Ferro-Giconi/Neopixel-bitmap/NeopixelBitmap.py

# Waveshare 160 Neopixel Board Basic
# Tony Goodhew 19th April 2022 for thepihut.com
import array
import utime
from machine import ADC, Pin
import rp2
import random
import math
import micropython
import _thread


# ==================================== battery ===================================
# reads the battery voltage on pin GP26 which is ADC0 on the Tiny2040
vsys = ADC(26)
# conversion factor to convert the output into a voltage. This uses a voltage
# divider to divide the voltage reading in half so it multiplies by 2.
conversion_factor = 2 * 3.3 / 65535
# these still need to be tuned based on what the ADC pin actually sees
full_battery = 4.2
empty_battery = 3.3
# convert the raw ADC read into a voltage, and then a percentage
battery_voltage = vsys.read_u16() * conversion_factor
battery_percentage = 100 * ((battery_voltage - empty_battery) / (full_battery - empty_battery))
if battery_percentage > 100:
    battery_percentage = 100.00

# battery voltage and percengate.
print('{:.2f}'.format(battery_voltage) + "v   -   " + '{:.0f}%'.format(battery_percentage))

# ==================================== screen stuff ===================================
# in variable names: w = width on the x axis and h = height on the y axis

# define how many Neopixels you have, width and height
# when connecting multiple Neopixels, arrange them in order from left to right, then top to bottom.
global screens_w
screens_w = 2
global screens_h
screens_h = 1
# if there is a gap between Neopixels, define the gap size in number of LEDs.
# this will take gaps into account when displaying images or text for a more normal look.
# gap_w = gap width in number of pixels between horizontally places Neopixels
# gap_h = gap height in number of pixels between vertically stacked Neopixels
# Integer only. Decimals will probably break it.
global gap_w
gap_w = 0
global gap_h
gap_h = 0

# I couldn't figure out how to check if the second thread is locked correctly so instead I'm using a global variable
global threadLocked
threadLocked = False

# Configure the number of WS2812 LEDs.
PIN_NUM = 6
brightness = 0.1
# set total number of LEDs. Each neopixel has 160 LEDs, 10H 16W.
screen_total_width = screens_w * 16 + (screens_w * gap_w - gap_w)
screen_total_height = screens_h * 10 + (screens_h * gap_h - gap_h)
NUM_LEDS = screen_total_width * screen_total_height

#calculates which X and Y cordinates will not be used if there are gaps defined
global missing_x
missing_x = []
for i in range(16,screen_total_width+1,1):
    ii = i
    while ii > 16:
        ii = ii - 16 - gap_w
    if ii <= 0:
        missing_x.append(i)

global missing_y
missing_y = []
for i in range(10,screen_total_height+1,1):
    ii = i
    while ii > 10:
        ii = ii - 10 - gap_h
    if ii <= 0:
        missing_y.append(i)

# Boilerplate Neopixel driver for RP2040
@rp2.asm_pio(sideset_init=rp2.PIO.OUT_LOW, out_shiftdir=rp2.PIO.SHIFT_LEFT, autopull=True, pull_thresh=24)
def ws2812():
    T1 = 2
    T2 = 5
    T3 = 3
    wrap_target()
    label("bitloop")
    out(x, 1)               .side(0)    [T3 - 1]
    jmp(not_x, "do_zero")   .side(1)    [T1 - 1]
    jmp("bitloop")          .side(1)    [T2 - 1]
    label("do_zero")
    nop()                   .side(0)    [T2 - 1]
    wrap()

# Create the StateMachine with the ws2812 program, outputting on pin
# You can also increase the frequency to improve performance by 1-2ms
sm = rp2.StateMachine(0, ws2812, freq=8_000_000, sideset_base=Pin(PIN_NUM))

# Start the StateMachine, it will wait for data on its FIFO.
sm.active(1)

# Display a pattern on the LEDs via an array of LED RGB values.
ar = array.array("I", [0 for _ in range(NUM_LEDS)])

####################### Functions ##############################

def pixels_show():
    dimmer_ar = array.array("I", [0 for _ in range(NUM_LEDS)])
    for i,c in enumerate(ar):
        r = int(((c >> 8) & 0xFF) * brightness)
        g = int(((c >> 16) & 0xFF) * brightness)
        b = int((c & 0xFF) * brightness)
        dimmer_ar[i] = (g<<16) + (r<<8) + b
    sm.put(dimmer_ar, 8)

def pixels_set(i, colour):
    ar[i] = (colour[1]<<16) + (colour[0]<<8) + colour[2]

def xy_set(x, y, colour):
    #check if a pixel is valid and set it if it is
    if valid_pixel(x,y):
        xy_set_valid(x, y, colour)

def xy_set_valid(x, y, colour):
    # +1 to x and y allows me to do pixel math in this function starting at 1 when the input x and y start at 0.
    # it's just easier for me to figure out the math that way.
    
    x = x + 1
    y = y + 1

    screen_x = 1
    screen_y = 1
    xx = x
    yy = y
    while xx > 16:
        screen_x = screen_x + 1
        xx = xx - 16 - gap_w
    while yy > 10:
        screen_y = screen_y + 1
        yy = yy - 10 - gap_h
    screen_number = screen_x + ((screen_y - 1) * screens_w)
    
    #calculate which pixel to set on which Neopixel
    pos = ((screen_number - 1) * 160) + (xx - 1) + (yy - 1) * 16
    pixels_set(pos, colour)

# it seems silly to do this but anything that can save an operation two in the valid pixel check will
# help improve how many μs each frame takes to display
global screen_total_width_minus_one
screen_total_width_minus_one = screen_total_width - 1
global screen_total_height_minus_one
screen_total_height_minus_one = screen_total_height - 1
def valid_pixel(x,y):
    # check if a pixel is valid
    valid_pixel = True
    # Check if the pixel you want to set is outside the size of the
    # screen to avoid wasting CPU cycles on pixels that you can't see
    if (x<0) or (y<0) or (x > screen_total_width_minus_one) or (y > screen_total_height_minus_one):
        valid_pixel = False
    # If you configured a gap between neopixels, check if the pixel is on a gap
    if valid_pixel:
        for i in missing_x:
            if x == i:
                valid_pixel = False
        for i in missing_y:
            if y == i:
                valid_pixel = False
    return valid_pixel

def pixels_fill(colour):
    _thread.start_new_thread(pixels_fill_thread2,((colour),))
    for i in range(math.ceil(len(ar)/2)):
        pixels_set(i, colour)
    # wait for the second thread to finish before continuing
    while threadLocked:
        utime.sleep_ms(1)

def pixels_fill_thread2(colour):
    global threadLocked
    threadLocked = True
    for i in range(math.ceil(len(ar)/2),len(ar)):
        pixels_set(i, colour)
    threadLocked = False
    _thread.exit()

def clear():
    colour = (0,0,0)
    pixels_fill(colour)
    
def rect(x,y,w,h,r,g,b):
    # Hollow square at (x,y), w pixels wide coloured (r,g,b)
    _thread.start_new_thread(rect_threads,(x,y,w,h,r,g,b,1))
    rect_threads(x,y,w,h,r,g,b,0)
    while threadLocked:
        utime.sleep_ms(1)

def rect_threads(x,y,w,h,r,g,b,threadNum):
    if threadNum:
        global threadLocked
        threadLocked = True
        cc = (r,g,b)
        for i in range(x,x+w):
            if valid_pixel(i,y):
                xy_set_valid(i,y,cc)       # Top
            if valid_pixel(i,y+h-1):
                xy_set_valid(i,y+h-1,cc)   # Bottom
    else:
        cc = (r,g,b)
        for i in range(y+1,y+h):
            if valid_pixel(x,i):
                xy_set_valid(x,i,cc)       # Left
            if valid_pixel(x+w-1,i):
                xy_set_valid(x+w-1,i,cc)   # Right
    if threadNum:
        threadLocked = False

def vert(x,y,l,r,g,b):
    # Vertical line at (x,y) of length l coloured (r,g,b)
    cc = (r,g,b)
    for i in range(l):
        if valid_pixel(x,i):
            xy_set_valid(x,i,cc)

def horiz(x,y,l,r,g,b):
    # Horizontal line from (x,y) of length l coloured (r,g,b)
    cc = (r,g,b)
    for i in range(l):
        if valid_pixel(i+x,y):
            xy_set_valid(i+x,y,cc)

def bitmap_set_fast(x,y,w,h,r,g,b):
    # bitmap_set(x_coordinate, y_coordinate, bmp_width, bmp_height, bmp_red, bmp_green, bmp_blue)
    # set the pixels for a bitmap. Treats 
    # start at pixel zero
    PxNum = 0
    for i in range(h):
        for j in range(w):
            if valid_pixel(j+x,i+y):
                rr = r[PxNum]
                gg = g[PxNum]
                bb = b[PxNum]
                # use the heavily modified xy_set to set each pixel
                xy_set_valid(j+x,i+y,(rr,gg,bb))
            PxNum = PxNum + 1

def bitmap_set24(x,y,ia,ga=1,br=1,tr=False):
    # bitmap_set(x_coord, y_coord, image_array, gama, brightness, transparency)
    # use for placing a 24 bit bitmap somewhere on screen.
    # start a thread to process the lower half of the pixels

    _thread.start_new_thread(bitmap_set24_threads,(x,y,ia,ga,br,tr,1))
    # start a the function to run at the same time as the thread to process the upper half of the pixels
    bitmap_set24_threads(x,y,ia,ga,br,tr,0)
    # wait for the thread to finish if it isn't done yet
    while threadLocked:
        utime.sleep_ms(1)

def bitmap_set24_threads(x,y,ia,ga,br,tr,threadNum):
    # do not call this function directly. This is used by bitmap_set24 to run my innefficient code on
    # two cores at once to improve performance
    w = ia[0][0]
    h = ia[1][0]
    r = ia[2]
    g = ia[3]
    b = ia[4]
    if threadNum:
        global threadLocked
        threadLocked = True
        PxNum = w*math.ceil(h/2)
        range1 = math.ceil(h/2)
        range2 = h
    else:
        PxNum = 0
        range1 = 0
        range2 = math.ceil(h/2)
    for i in range(range1,range2,1):
        for j in range(w):
            if valid_pixel(j+x,i+y):
            # if transparency is disabled, or if it is enabled and the r,g,b isn't 0,0,0, draw the pixel.
                if tr and (r[PxNum]+g[PxNum]+b[PxNum] > 0) or (not tr):
                    # compress the data range from 0-255 to 0-246 to compensate for the 0-9 pixels all being black
                    rr = r[PxNum]*246/255
                    gg = g[PxNum]*246/255
                    bb = b[PxNum]*246/255
                    # adjust the brightness
                    rr = rr*br
                    gg = gg*br
                    bb = bb*br
                    # This is a crude gama adjustment formula which can help make bitmaps look more normal instead of washed out
                    rr = math.pow(rr,ga) * 246 / math.pow(246,ga)
                    gg = math.pow(gg,ga) * 246 / math.pow(246,ga)
                    bb = math.pow(bb,ga) * 246 / math.pow(246,ga)
                    # undo the compression
                    rr = math.ceil(rr+9)
                    gg = math.ceil(gg+9)
                    bb = math.ceil(bb+9)
                    # use the heavily modified xy_set to set each pixel
                    xy_set_valid(j+x,i+y,(rr,gg,bb))
            PxNum = PxNum + 1
    if threadNum == 1:
        threadLocked = False
        _thread.exit()

def bitmap_set1(x,y,ia,r,g,b,tr=False):
    # bitmap_set(x_coord, y_coord, image_array,color,transparency)
    # Sets a 1 bit bitmap using a defined color
    # start a thread to process the lower half of the pixels

    _thread.start_new_thread(bitmap_set1_threads,(x,y,ia,r,g,b,tr,1))
    # start a the function to run at the same time as the thread to process the upper half of the pixels
    bitmap_set1_threads(x,y,ia,r,g,b,tr,0)
    # wait for the thread to finish if it isn't done yet
    while threadLocked:
        utime.sleep_ms(1)

            
def bitmap_set1_threads(x,y,ia,r,g,b,tr,threadNum):
    # bitmap_set(x_coord, y_coord, image_array,color,transparency)
    # Sets a 1 bit bitmap using a defined color
    w = ia[0][0]
    h = ia[1][0]
    p = ia[2]
    if threadNum:
        global threadLocked
        threadLocked = True
        PxNum = w*math.ceil(h/2)
        range1 = math.ceil(h/2)
        range2 = h
    else:
        PxNum = 0
        range1 = 0
        range2 = math.ceil(h/2)
    for i in range(range1,range2,1):
        for j in range(w):
            if valid_pixel(j+x,i+y):
                if tr and p[PxNum] or not tr and j < 33:
                    xy_set_valid(j+x,i+y,(p[PxNum]*r,p[PxNum]*g,p[PxNum]*b))
            PxNum = PxNum + 1
    if threadNum:
        threadLocked = False

def button_handler():
    asdf = "nothing here yet"

def adjust_gama_list(color,ga):
    # this is a crude way to adjust the gama so that images don't display blown out on the screen
    for i in range(len(color)):
        color[i] = math.trunc(math.pow(color[i],ga) * 255 / math.pow(255,ga))
    return(color)

def adjust_gama(color,ga):
    # this is a crude way to adjust the gama so that images don't display blown out on the screen
    color = math.trunc(math.pow(color,ga) * 255 / math.pow(255,ga))
    return(color)

# ======================= BUTTON HANDLING ========================
button4 = Pin(4, Pin.IN, Pin.PULL_UP)
button5 = Pin(5, Pin.IN, Pin.PULL_UP)

button_presses = 0 # the count of times the button has been pressed
button_presses_last = 0
button_last_time = 0 # the last time we pressed the button

# This function gets called every time the button is pressed.
def button_pressed(pin):
    global button_presses, button_last_time
    button_new_time = utime.ticks_ms()
    print(str(pin))
    # check the time for simple debouncing to prevent the button from triggering like 20 times when pressed
    if (button_new_time - button_last_time) > 200:
        # this should be pin.id but it does not work
        if '5' in str(pin):
            button_presses +=1
        elif '4' in str(pin):
            button_presses -=1
        button_last_time = button_new_time

def buttonBreak():
    # simple function to make code more readable in the animations
    global button_presses, button_presses_last
    if not button_presses == button_presses_last:
        return True

button4.irq(trigger=Pin.IRQ_FALLING, handler = button_pressed)
button5.irq(trigger=Pin.IRQ_FALLING, handler = button_pressed)

# ======================= BITMAP DATA ======================= 

# define the quantity of bitmaps that will be defined starting at 0
qtyOfBitmaps = 1
bitmap = [[],[],[],[],[]]


# test image of jayde's head
# Array for bitmap 0
# This array is stored as [width],[height],[R_list],[G_list],[B_list]
bitmap[0] = [[16],[20],[0,0,0,0,3,70,70,70,70,70,70,70,70,70,70,70,0,0,0,3,70,70,70,70,70,70,70,70,70,70,3,70,0,0,3,70,70,70,70,70,70,70,70,70,70,3,70,70,0,3,70,70,70,70,70,70,70,70,70,70,70,3,70,3,0,3,70,70,70,70,70,70,70,70,70,70,147,3,70,3,3,70,70,70,70,70,70,70,70,70,70,3,147,3,70,3,0,3,70,70,70,70,70,70,70,70,3,3,3,0,3,0,0,3,147,70,3,70,70,70,70,70,3,0,0,0,0,0,3,147,147,147,3,147,70,70,70,70,3,0,0,0,0,0,3,147,147,3,147,147,147,147,70,70,3,0,0,0,0,0,3,147,147,3,147,147,147,147,147,147,3,0,0,0,0,0,3,147,147,3,147,147,147,147,147,147,3,0,0,0,0,0,0,3,147,147,3,147,147,147,147,3,0,0,0,0,0,0,0,3,147,147,3,147,147,147,147,3,0,0,0,0,0,0,3,147,147,147,3,147,147,147,147,3,0,0,0,0,0,0,3,147,147,147,3,147,147,147,147,3,0,0,0,0,0,0,3,147,147,3,147,147,147,147,147,3,0,0,0,0,0,0,0,3,3,0,3,3,147,3,3,0,0,0,0,0,0,0,0,0,0,0,0,3,147,3,0,0,0,0,0,0,0,0,0,0,0,0,0,0,3,0,0,0,0,0,0,0,0,0],[0,0,0,0,3,34,34,34,34,34,34,34,34,34,34,34,0,0,0,3,34,34,34,34,34,34,34,34,34,34,3,34,0,0,3,34,34,34,34,34,34,34,34,34,34,3,34,34,0,3,34,34,34,34,34,34,34,34,34,34,34,3,34,3,0,3,34,34,34,34,34,34,34,34,34,34,225,3,34,3,3,34,34,34,34,34,34,34,34,34,34,3,225,3,34,3,0,3,34,34,34,34,34,34,34,34,3,3,3,0,3,0,0,3,225,34,3,34,34,34,34,34,3,0,0,0,0,0,3,225,225,225,3,225,34,34,34,34,3,0,0,0,0,0,3,225,225,3,225,225,225,225,34,34,3,0,0,0,0,0,3,225,225,3,225,225,225,225,225,225,3,0,0,0,0,0,3,225,225,3,225,225,225,225,225,225,3,0,0,0,0,0,0,3,225,225,3,225,225,225,225,3,0,0,0,0,0,0,0,3,225,225,3,225,225,225,225,3,0,0,0,0,0,0,3,225,225,225,3,225,225,225,225,3,0,0,0,0,0,0,3,225,225,225,3,225,225,225,225,3,0,0,0,0,0,0,3,225,225,3,225,225,225,225,225,3,0,0,0,0,0,0,0,3,3,0,3,3,225,3,3,0,0,0,0,0,0,0,0,0,0,0,0,3,225,3,0,0,0,0,0,0,0,0,0,0,0,0,0,0,3,0,0,0,0,0,0,0,0,0],[0,0,0,0,3,85,85,85,85,85,85,85,85,85,85,85,0,0,0,3,85,85,85,85,85,85,85,85,85,85,3,85,0,0,3,85,85,85,85,85,85,85,85,85,85,3,85,85,0,3,85,85,85,85,85,85,85,85,85,85,85,3,85,3,0,3,85,85,85,85,85,85,85,85,85,85,216,3,85,3,3,85,85,85,85,85,85,85,85,85,85,3,216,3,85,3,0,3,85,85,85,85,85,85,85,85,3,3,3,0,3,0,0,3,216,85,3,85,85,85,85,85,3,0,0,0,0,0,3,216,216,216,3,216,85,85,85,85,3,0,0,0,0,0,3,216,216,3,216,216,216,216,85,85,3,0,0,0,0,0,3,216,216,3,216,216,216,216,216,216,3,0,0,0,0,0,3,216,216,3,216,216,216,216,216,216,3,0,0,0,0,0,0,3,216,216,3,216,216,216,216,3,0,0,0,0,0,0,0,3,216,216,3,216,216,216,216,3,0,0,0,0,0,0,3,216,216,216,3,216,216,216,216,3,0,0,0,0,0,0,3,216,216,216,3,216,216,216,216,3,0,0,0,0,0,0,3,216,216,3,216,216,216,216,216,3,0,0,0,0,0,0,0,3,3,0,3,3,216,3,3,0,0,0,0,0,0,0,0,0,0,0,0,3,216,3,0,0,0,0,0,0,0,0,0,0,0,0,0,0,3,0,0,0,0,0,0,0,0,0]]

# test image of jayde's hoof
# Array for bitmap 1
# This array is stored as [width],[height],[R_list],[G_list],[B_list]
bitmap[1] = [[16],[20],[187,176,154,94,41,9,0,0,1,12,25,44,66,89,117,136,193,180,151,91,43,13,3,3,7,20,30,46,65,85,107,125,203,187,143,87,46,19,9,8,18,32,39,50,64,77,85,99,204,183,132,82,49,25,13,11,23,40,44,49,58,65,60,70,195,168,118,76,51,31,17,12,26,46,46,44,47,47,34,38,182,152,106,71,52,34,21,20,34,48,46,39,36,29,7,0,167,140,102,69,51,33,27,32,43,47,44,35,27,14,0,0,165,142,110,79,56,36,34,41,49,47,41,31,18,2,0,0,177,157,127,98,65,41,42,48,50,46,38,27,9,0,0,0,183,168,147,119,77,50,47,48,46,41,33,22,4,0,0,0,183,175,166,140,90,61,48,41,37,31,27,16,4,0,0,0,178,174,173,153,102,73,50,34,26,22,22,12,5,0,0,0,170,167,169,159,113,84,54,30,19,18,19,12,4,0,0,0,168,164,168,161,119,89,56,29,17,21,20,14,4,0,0,0,171,166,171,160,121,89,57,32,23,28,25,17,4,0,0,0,173,166,169,153,114,84,56,35,31,37,32,22,8,2,2,4,172,164,162,139,98,73,51,36,39,45,39,28,15,7,7,11,172,163,153,122,81,60,43,32,40,50,46,34,23,16,16,21,175,163,144,104,66,48,33,24,35,51,51,40,31,24,24,30,176,163,140,93,57,41,27,18,32,52,54,43,34,28,28,33],[0,0,5,16,13,13,28,40,45,50,49,54,69,90,104,104,0,1,7,17,14,14,29,41,49,58,59,69,92,115,126,135,0,3,11,18,17,16,30,43,58,71,78,94,125,150,160,177,6,12,20,22,20,19,32,50,72,94,112,138,164,179,194,209,16,23,29,28,23,23,37,60,90,120,149,183,201,203,226,233,25,33,35,31,25,26,45,76,112,150,189,214,224,224,241,241,34,43,40,33,27,29,57,95,135,181,227,236,236,242,242,236,45,55,54,45,36,41,75,115,158,207,246,247,244,246,237,227,58,68,71,61,49,57,95,136,180,229,251,249,250,239,226,216,74,82,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





# ================  Replace everyting before this line  ================
# ================ with the output from the RGB program ================

# Due to memory constaints and crappy code, loading multiple "large" bitmaps is problematic.
# For some reason, just loading a bitmap doesn't use much ram, but modifying it uses a lot.
# Because of this, adjuustments to images should be used sparingly except as needed to improve
# frame times during render.
# bmpR[0] = adjust_gama_list(bmpR[0],1.8)
# bmpG[0] = adjust_gama_list(bmpG[0],1.8)
# bmpB[0] = adjust_gama_list(bmpB[0],1.8)


micropython.mem_info()
TimeCounter = utime.ticks_ms()
print(utime.ticks_ms()-TimeCounter)

# ========= Define animation code here as functions ========
# animations that you want to be interrupted by buttons should have the one line
# if buttonBreak():break
# in the animation's loops to make sure the animation can be stopped in a timely manner


def animation0():
    # for this example you need one neopixel
    # set screens_h = 1
    # set screens_w = 1
    # Displays the text "load..." which I created thinking there might be a perceptible loading time
    # but there wasn't so it's just one of the example animations.
    TimeCounter = utime.ticks_ms()
    for i in range(17,-17,-1):
        clear()
        bitmap_set1(i,2,bitmap[2],40,0,40,False)
        pixels_show()
        # stop the animation if a button is pressed
        if buttonBreak():break
    print("Animation 0 took " + str(utime.ticks_ms()-TimeCounter) + "ms")

def animation1():    
    # for this example you need one neopixel
    # set screens_h = 1
    # set screens_w = 1
    TimeCounter = utime.ticks_ms()
    bg_pos = -12
    for i in range(12):
        # draw the background which is a tiled 12 pixel image
        for j in range(3):
            bitmap_set24(j*12+bg_pos,2,bitmap[4],1.8,.3)
        bg_pos = bg_pos + 1
        if bg_pos == 0:
            bg_pos = -12
        pixels_show()
        if buttonBreak():break
    print("Animation 1 took " + str(utime.ticks_ms()-TimeCounter) + "ms")

def animation2():
    # fancy scrolling text example with utime.sleep used to make frame times consistent
    # this uses all the CPU power because of the image size.

    # for this example, you need two neopixels to see it all
    # set screens_h = 1
    # set screens_w = 2
    TimeCounter = utime.ticks_ms()
    for sadfjhasd in range(1):
        bg_pos = -11
        for i in range(32,-82,-1):
            FrameTime = utime.ticks_ms()
            # draw the background which is a tiled 12 pixel image
            for j in range(4):
                bitmap_set24(j*12+math.floor(bg_pos),2,bitmap[4],1,1)
            bg_pos = bg_pos + .5
            if bg_pos == 0:
                bg_pos = -11
            # draw the text.
            bitmap_set1(i,2,bitmap[3],0,0,0,True)
            # draw black pixels to prevent the background from being visible once the text passes
            if i > 0:
                for j in range(2,8,1):
                    horiz(0,j,i,0,0,0)
            if i < 32-81:
                for j in range(2,8,1):
                    horiz(i+81,j,32-i-81,0,0,0)
            utime.sleep_ms(10 - (utime.ticks_ms() - FrameTime))
            pixels_show()
            if buttonBreak():break
    print("Animation 2 took " + str(utime.ticks_ms()-TimeCounter) + "ms")  

def animation3():
    # for this example, you need two neopixels to see it all
    # set screens_h = 2
    # set screens_w = 1
    TimeCounter = utime.ticks_ms()
    for i in range(17,-17,-1):
        # this example scrolls the bitmap from right to left over a static background
        # bitmap_set defines which bitmap to use.
        # normally clear() would be needed, but with a background it isn't needed so it is commented out
        # clear()
        bitmap_set24(0,0,bitmap[1],2,.3)
        # draw the bitmap over the background with black pixels treated as transparent
        bitmap_set24(i,0,bitmap[0],1.7,.8,True)
        # draw a few random pixels over the bitmap
        # the normal xy_set does not check if you are setting a valid pixel. xy_set_valid does. Use it for safety.
        for i in range(12):
            xy_set(math.ceil(screen_total_width*random.random()),math.ceil(screen_total_height*random.random()),(200,200,200))
        # display the result
        pixels_show()
        if buttonBreak():break
    print("Animation 3 took " + str(utime.ticks_ms()-TimeCounter) + "ms")


# ======================= Runs animations on a loop ==================
number_of_animations = 3
while True:
    if not button_presses_last == button_presses:
        # only clear the screen if the animation is changed, otherwise let the
        # animation handle its own screen clearing
        clear()
        button_presses_last = button_presses
    
    if button_presses < 0:
        button_presses = number_of_animations
    if button_presses > number_of_animations:
        button_presses = 0
        
    # play the selected animation
    eval('animation' + str(button_presses) + '()')
    
    
    
    
    
    

clear()
pixels_show()
